mbrennwa/OSDEHA/documentation/figures/CCS_Rsense_circuit.pdf

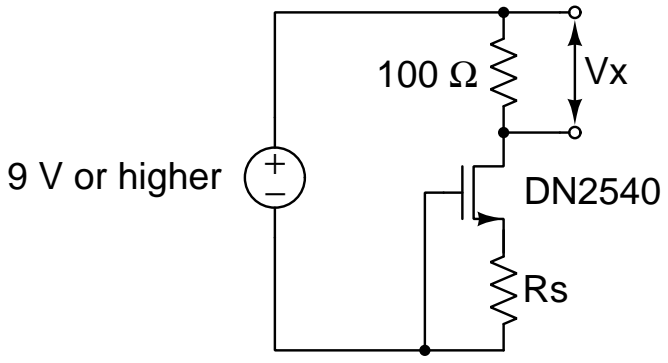
[picture p31: figure]
9 V or higher
