mbrennwa/OSDEHA/documentation/figures/6E5P_curves.pdf

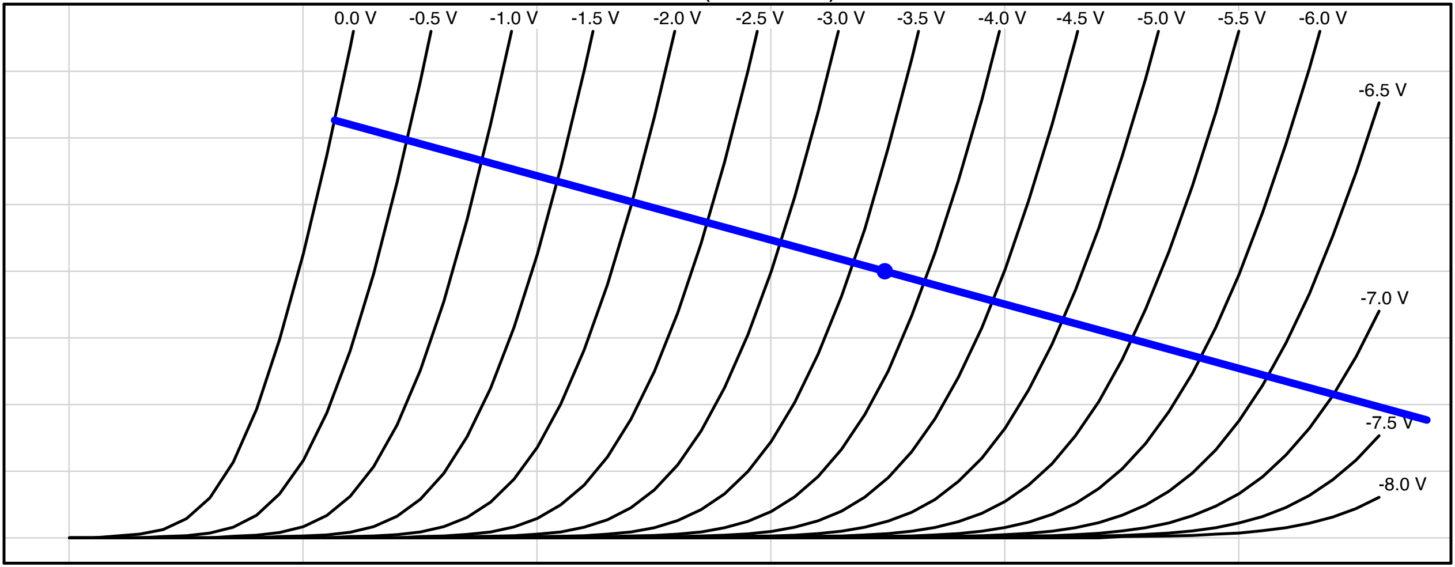
[picture p32: figure]

0 | 50 | 100 | 150 | 200 | 250

## ANODE-CATHODE VOLTAGE (V)

0.0

2.5

5.0

7.5

10.0

12.5

15.0

17.5

20.0

## ANODE CURRENT (mA)

0.0 V -0.5 V -1.0 V | -1.5 V -2.0 V -2.5 V | -3.0 V -3.5 V -4.0 V | -4.5 V -5.0 V -5.5 V | -6.0 V

# 6E5P (TRIODE)
