mbrennwa/OSDEHA/documentation/figures/activeload_concept.pdf

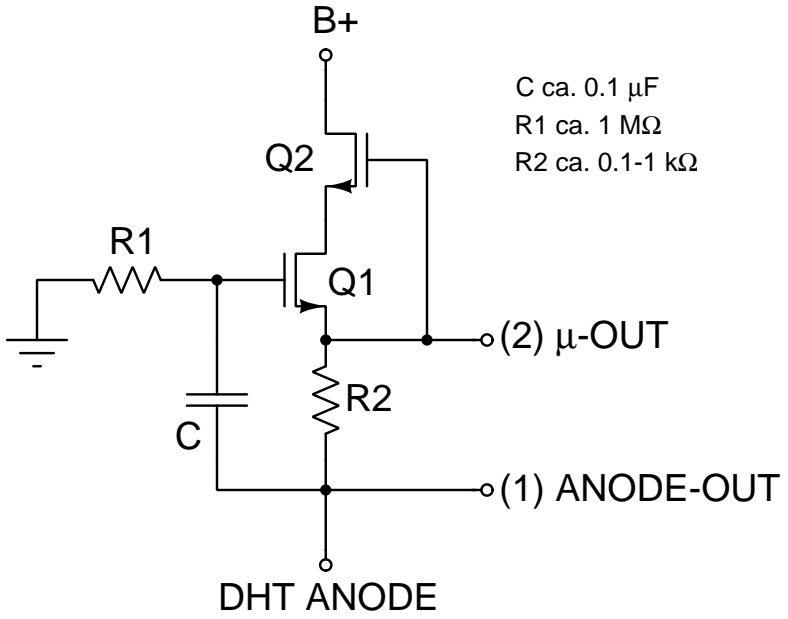
[picture p33: figure]
DHT ANODE; (2) µ-OUT; (1) ANODE-OUT
