mbrennwa/OSDEHA/datasheets/6E5P_curves.webp

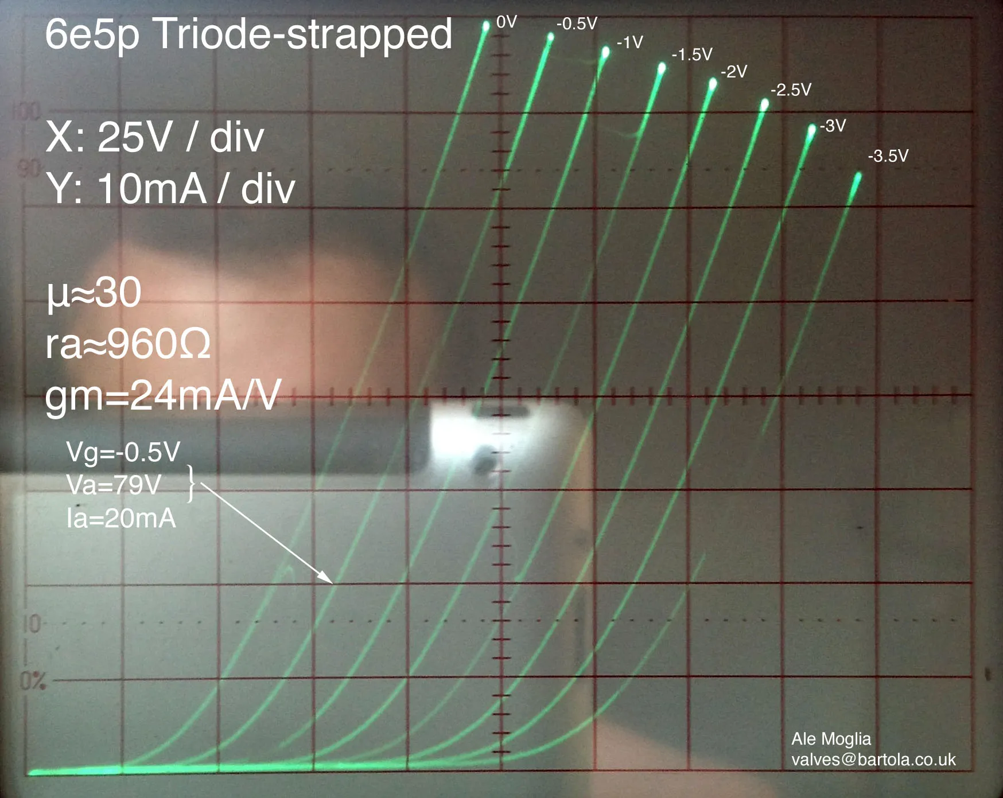
datasheets/6E5P_curves.webp
