mbrennwa/OSDEHA/datasheets/801A_Curves.png

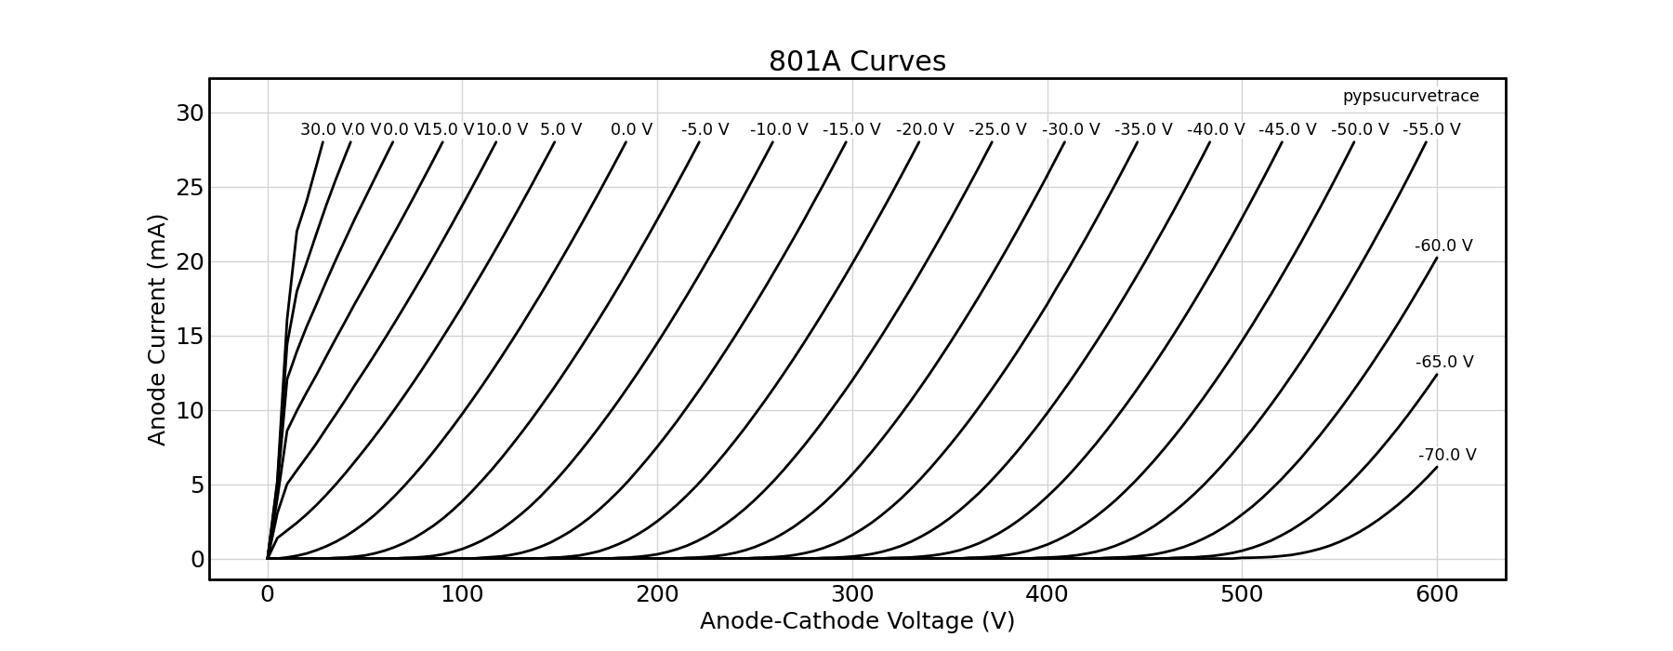
datasheets/801A_Curves.png
