mbrennwa/OSDEHA/datasheets/E180F_curves.png

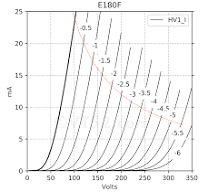
datasheets/E180F_curves.png
