mbrennwa/OSDEHA/datasheets/EF184_curves.jpg

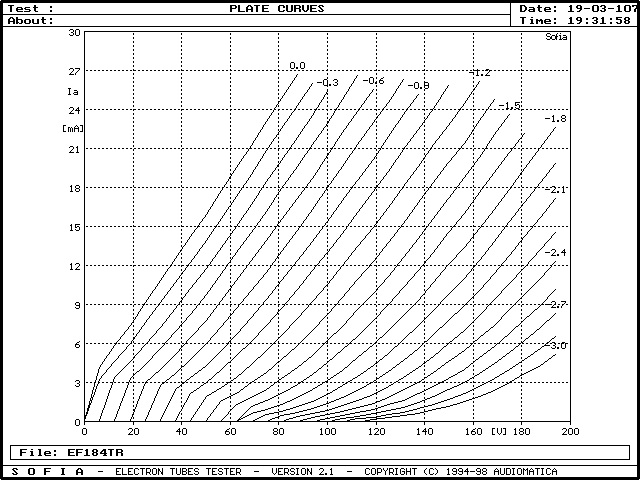
datasheets/EF184_curves.jpg
