mbrennwa/OSDEHA/datasheets/VT25_Curves.png

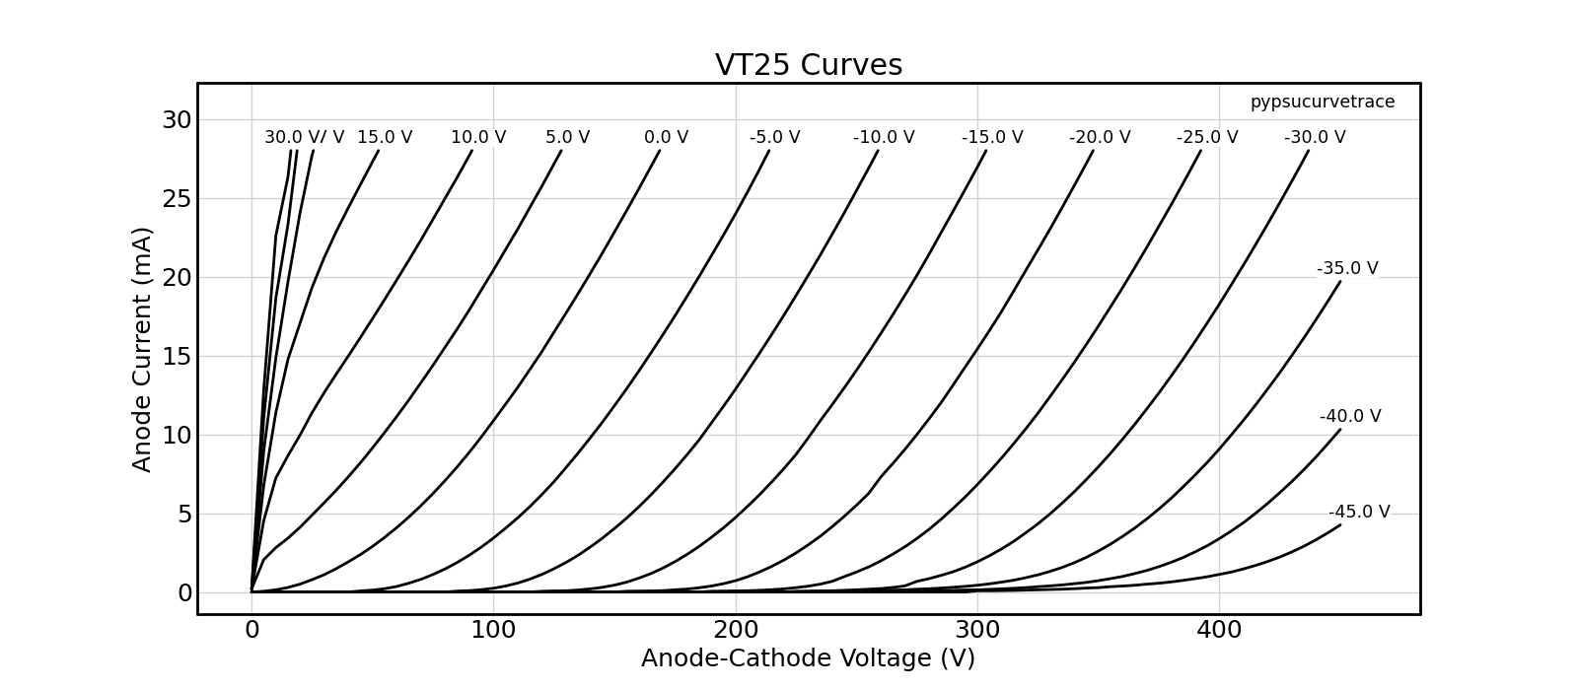
datasheets/VT25_Curves.png
