mbrennwa/OSDEHA/photos/DHT_gate_resistor_on_socket.jpg

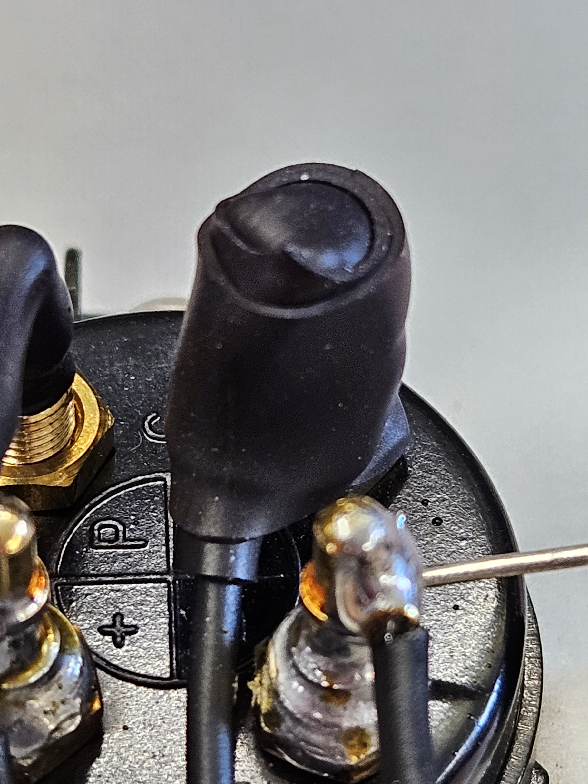
photos/DHT_gate_resistor_on_socket.jpg
