mbrennwa/OSDEHA/stuff/Ale_Moglia_stabilized_HV_for_ideas.webp

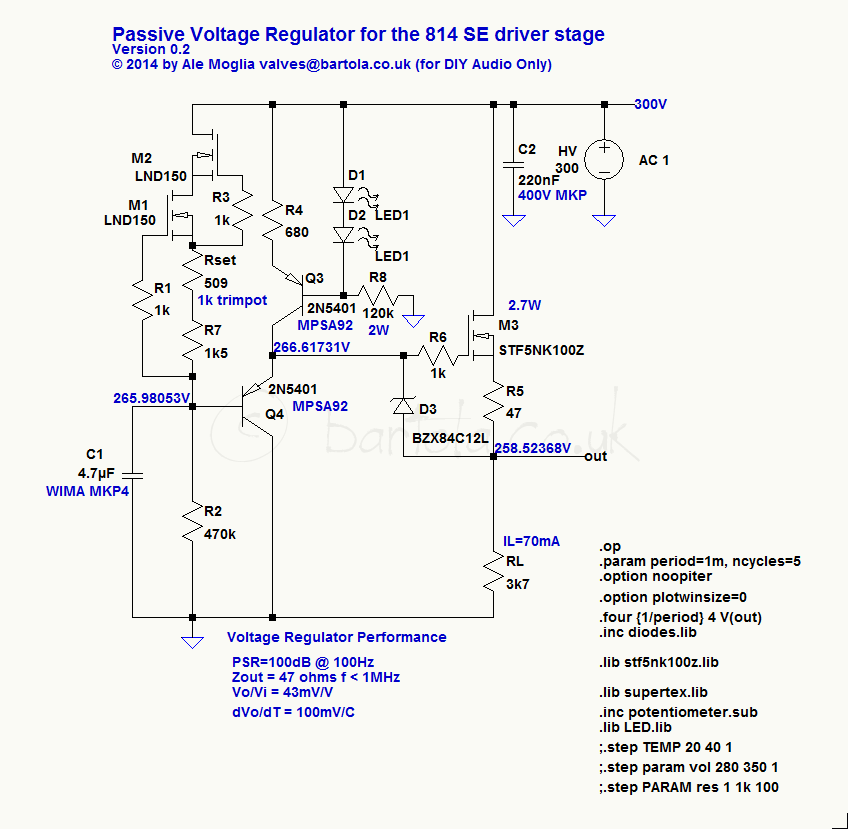
stuff/Ale_Moglia_stabilized_HV_for_ideas.webp
