mbrennwa/OSDEHA/stuff/current_time_physiological_safety/2880px-IEC_TS_60479-1_electric_shock_graph.svg.png

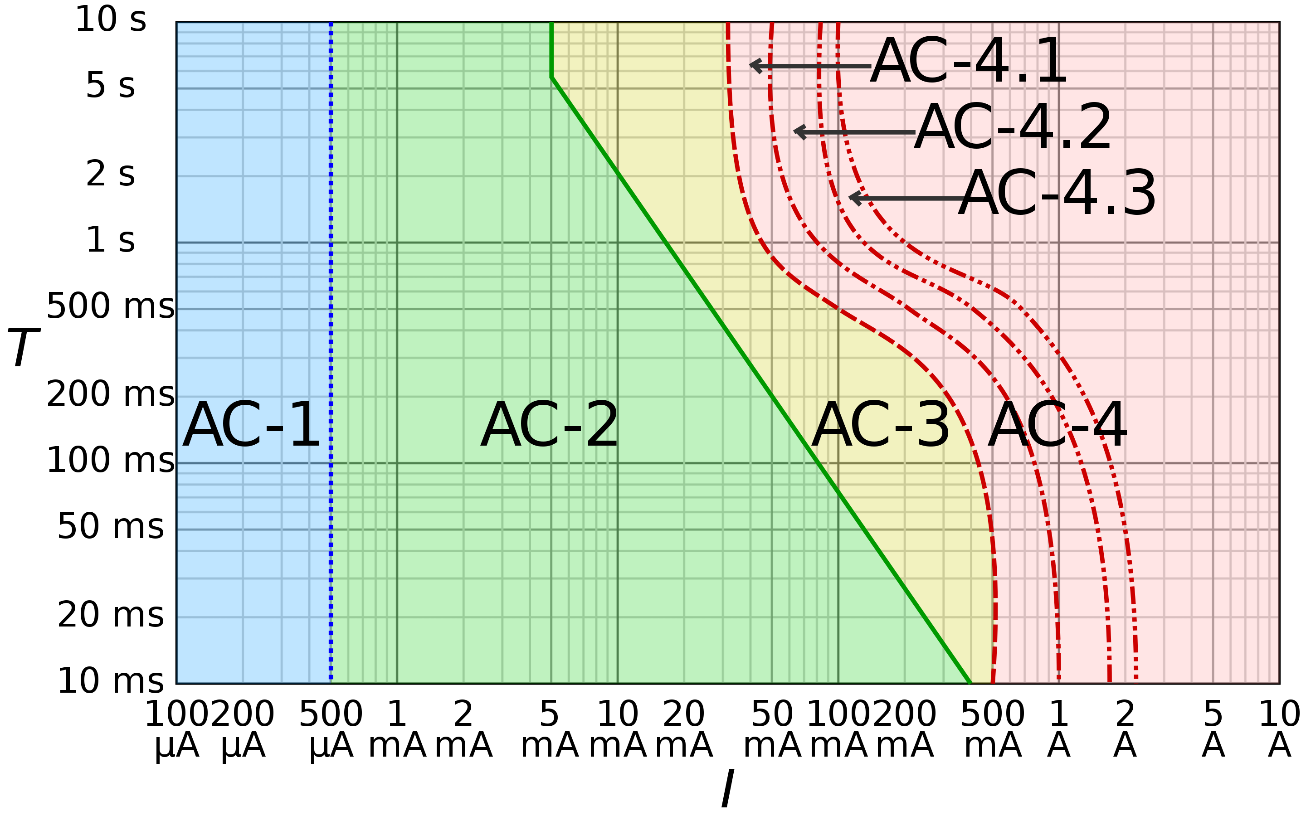
stuff/current_time_physiological_safety/2880px-IEC_TS_60479-1_electric_shock_graph.svg.png
