mbrennwa/OSDEHA/stuff/goldreference_PSU_GRHV_for_ideas.JPG

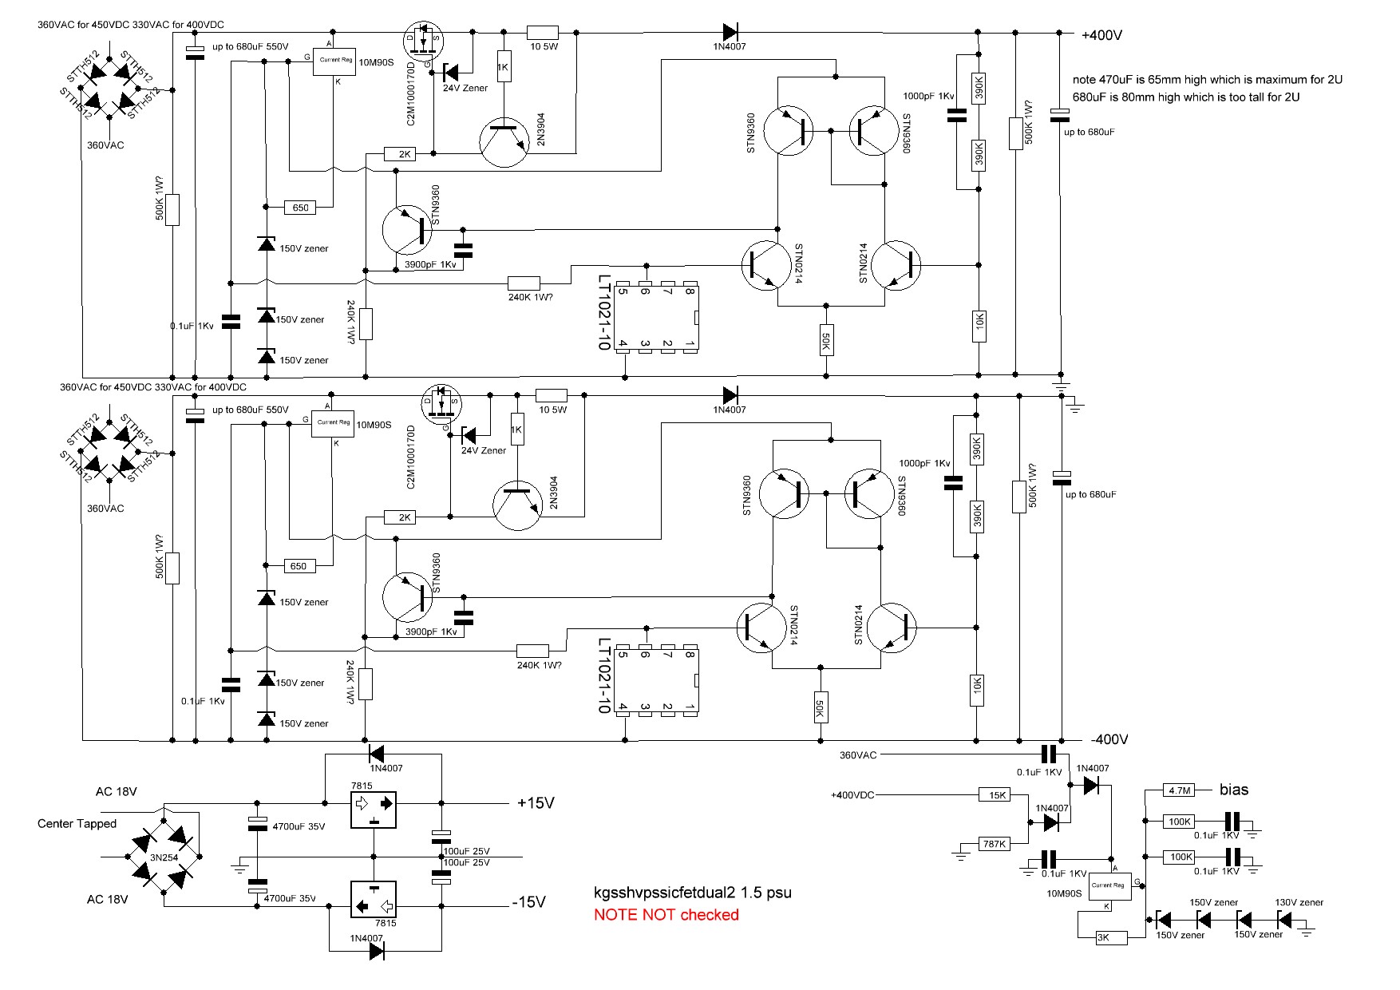
stuff/goldreference_PSU_GRHV_for_ideas.JPG
