mbrennwa/OSDEHA/stuff/rauenbühler_heater_delay_555.GIF

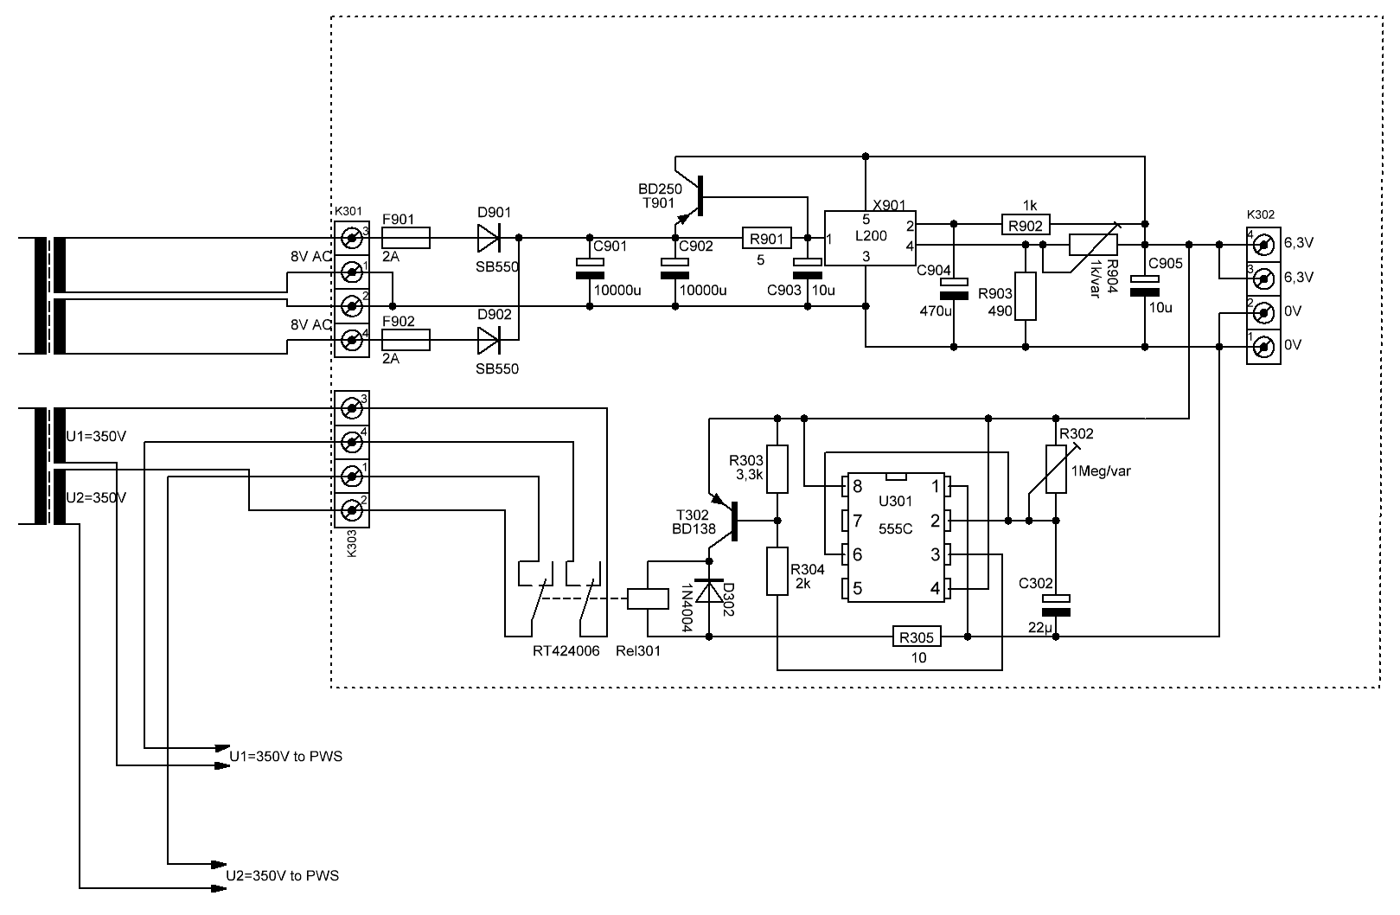
stuff/rauenbühler_heater_delay_555.GIF
