mbrennwa/OSDEHA/notes_and_measurements/2024-05-11/IPS_6E5P_No.5.6_notmatched/OSDEHA_IPS_IM_VOUT31.6.png

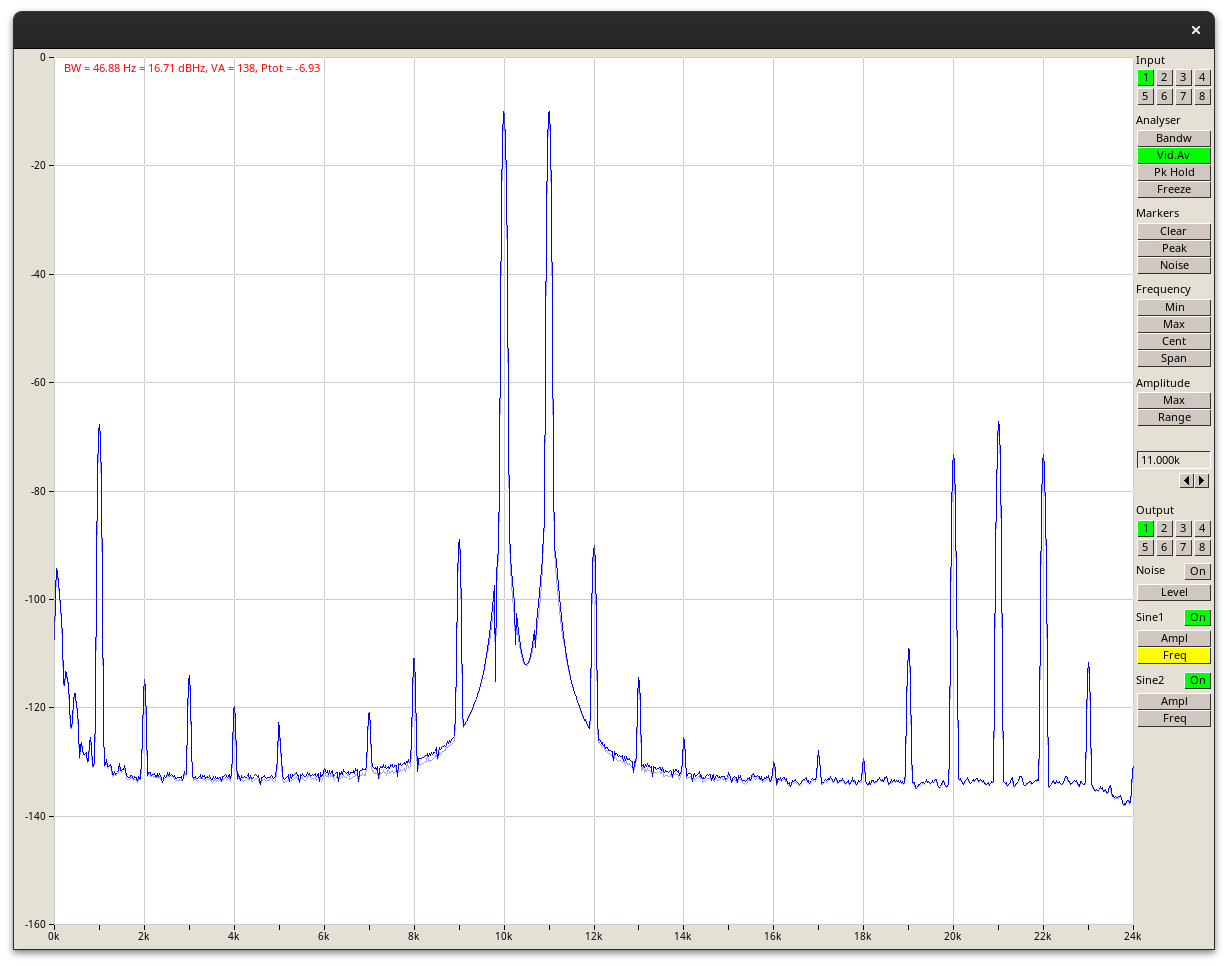
notes_and_measurements/2024-05-11/IPS_6E5P_No.5.6_notmatched/OSDEHA_IPS_IM_VOUT31.6.png
