mbrennwa/OSDEHA/notes_and_measurements/2024-05-11/IPS_6E5P_No.29.34.matched/OSDEHA_IPS_VOUT3.16.png

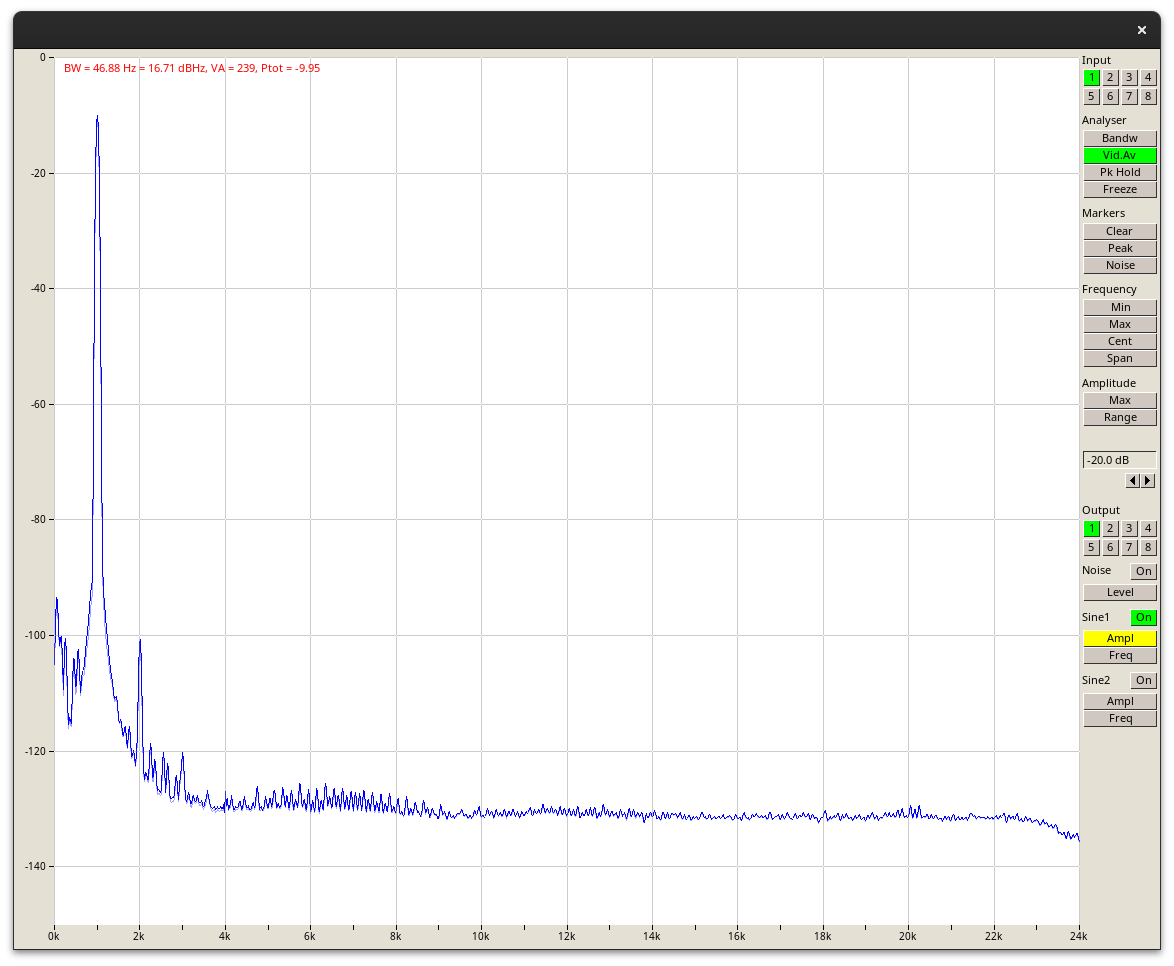
notes_and_measurements/2024-05-11/IPS_6E5P_No.29.34.matched/OSDEHA_IPS_VOUT3.16.png
