mbrennwa/OSDEHA/notes_and_measurements/harmonic_distortion/OSDEHA_MU-out_harmonics-1.png

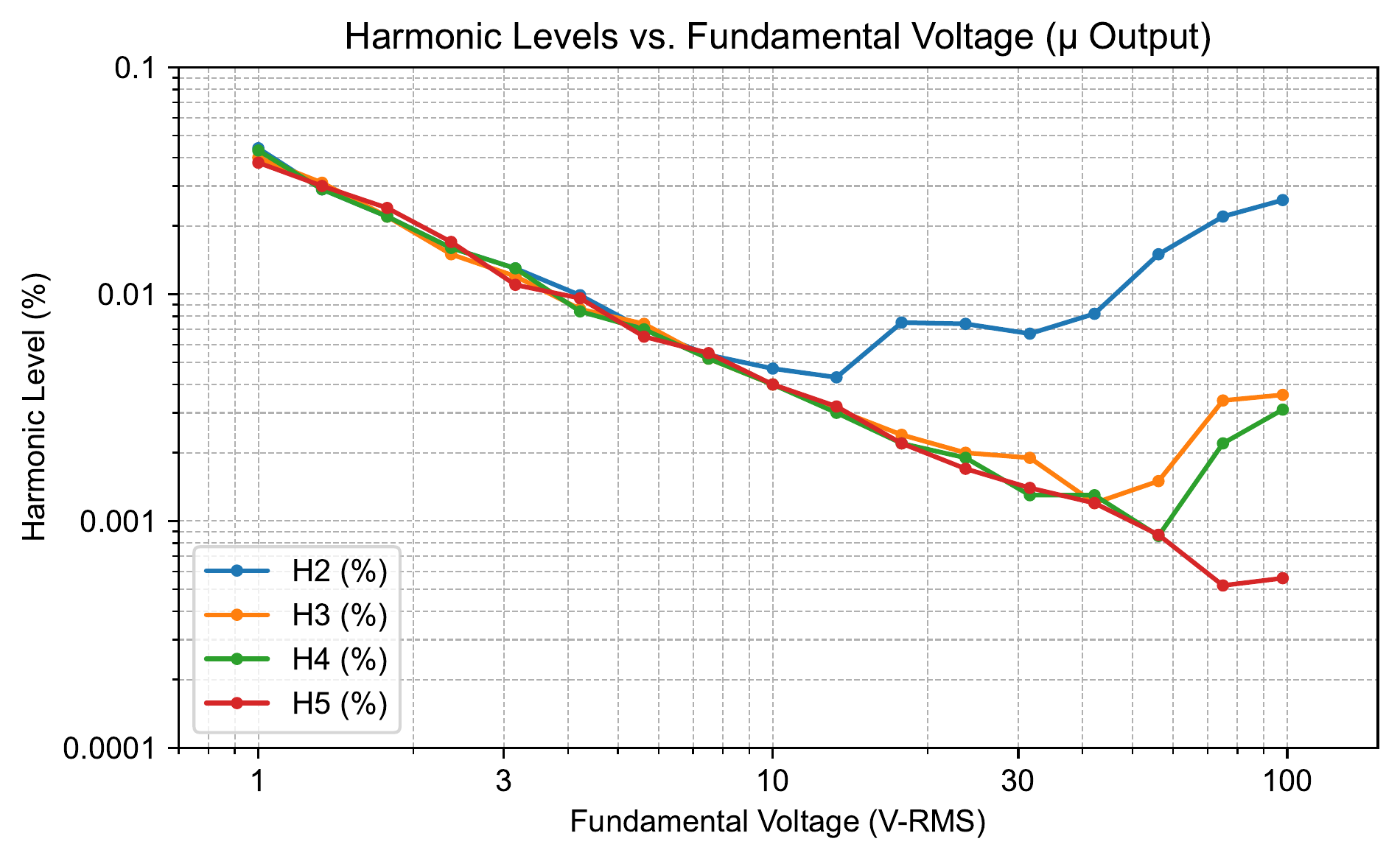
notes_and_measurements/harmonic_distortion/OSDEHA_MU-out_harmonics-1.png
