mbrennwa/OSDEHA/notes_and_measurements/input_tubes/6E5P_Ia10mA_Vg2V_Rk34k.png

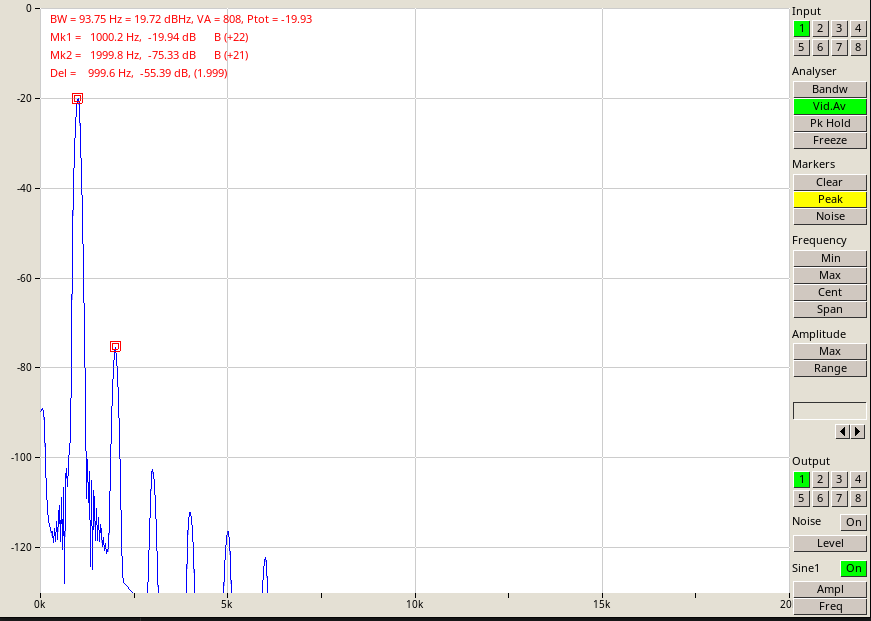
notes_and_measurements/input_tubes/6E5P_Ia10mA_Vg2V_Rk34k.png
