mbrennwa/OSDEHA/notes_and_measurements/input_tubes/6E5P_Ia10mA_Vg3V_Rk28k.png

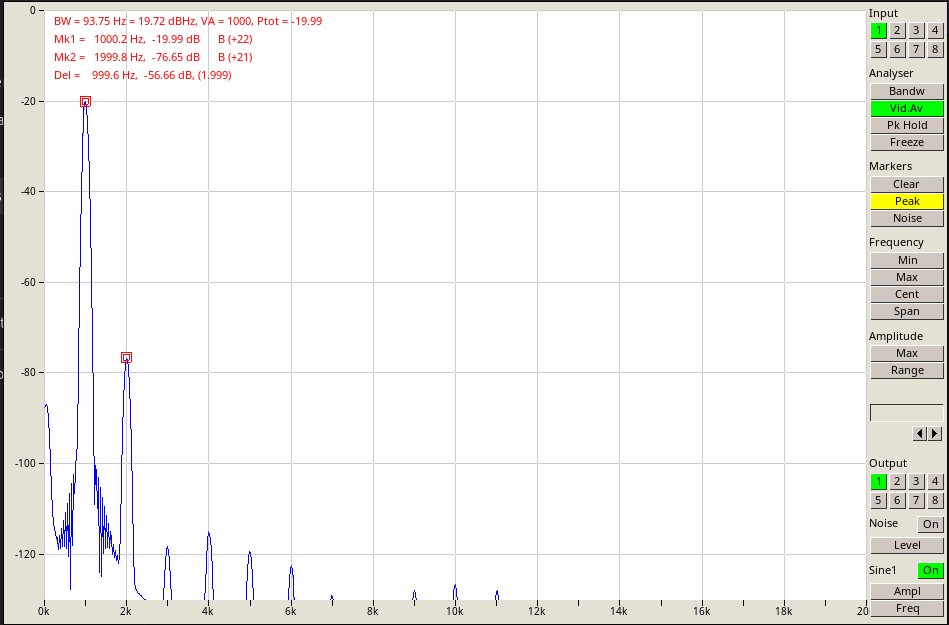
notes_and_measurements/input_tubes/6E5P_Ia10mA_Vg3V_Rk28k.png
