mbrennwa/OSDEHA/documentation/figures/801A_curves.pdf

25

801A

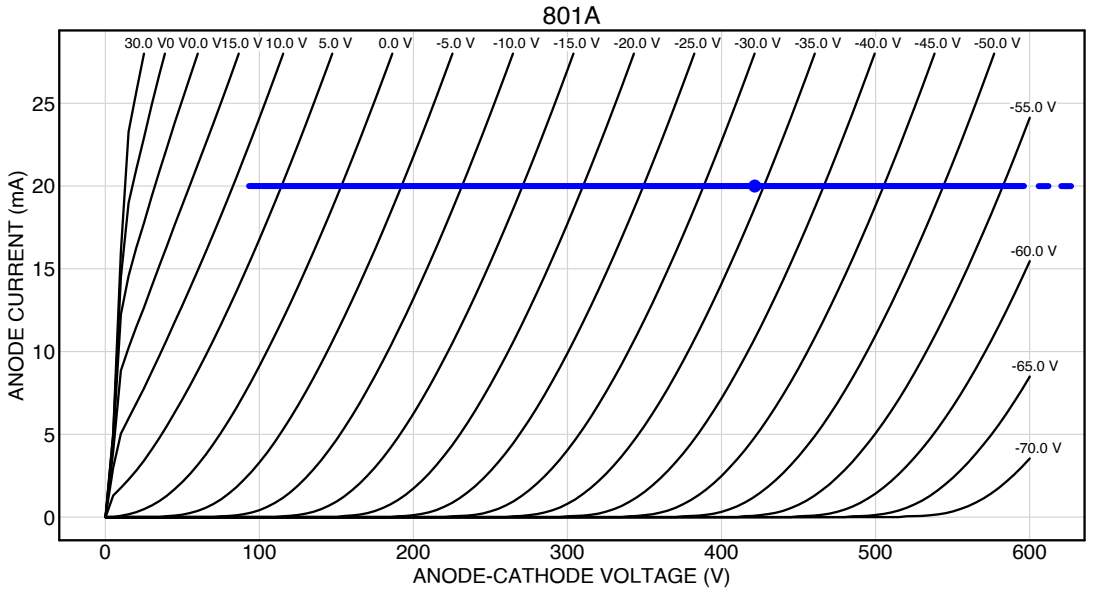
[picture p62: page 1]

ANODE CURRENT (mA)

ANODE-CATHODE VOLTAGE (V)
