mbrennwa/OSDEHA/documentation/figures/OPS_concept.pdf

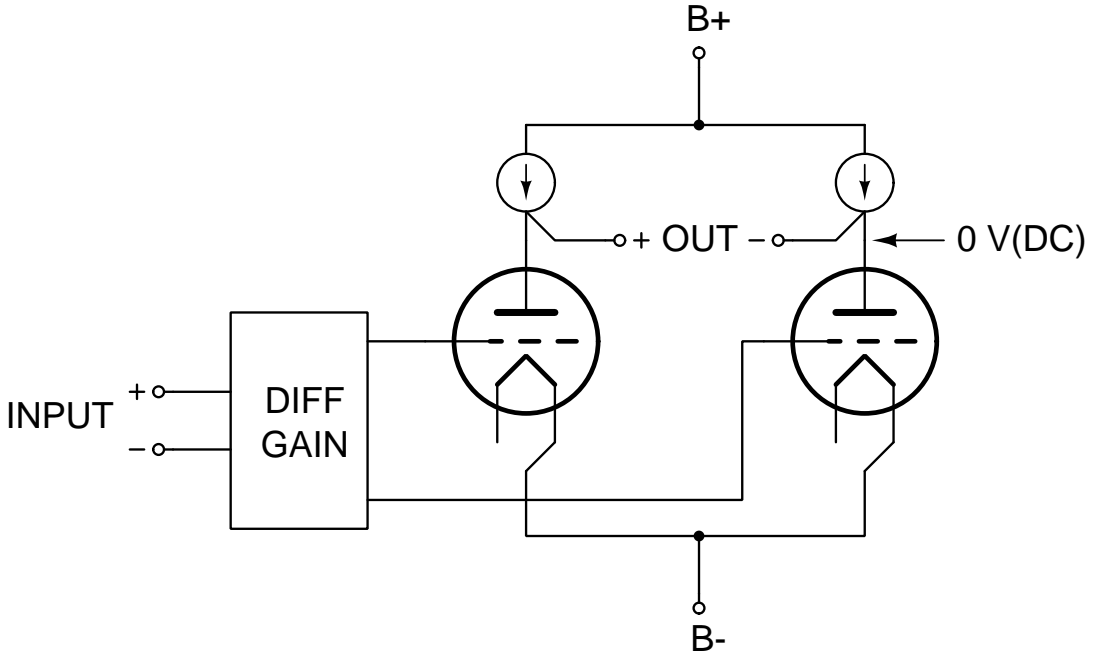
[picture p74: page 1]
OUT; DIFF GAIN; INPUT
