mbrennwa/OSDEHA/stuff/Baby_Huey_for_ideas.pdf

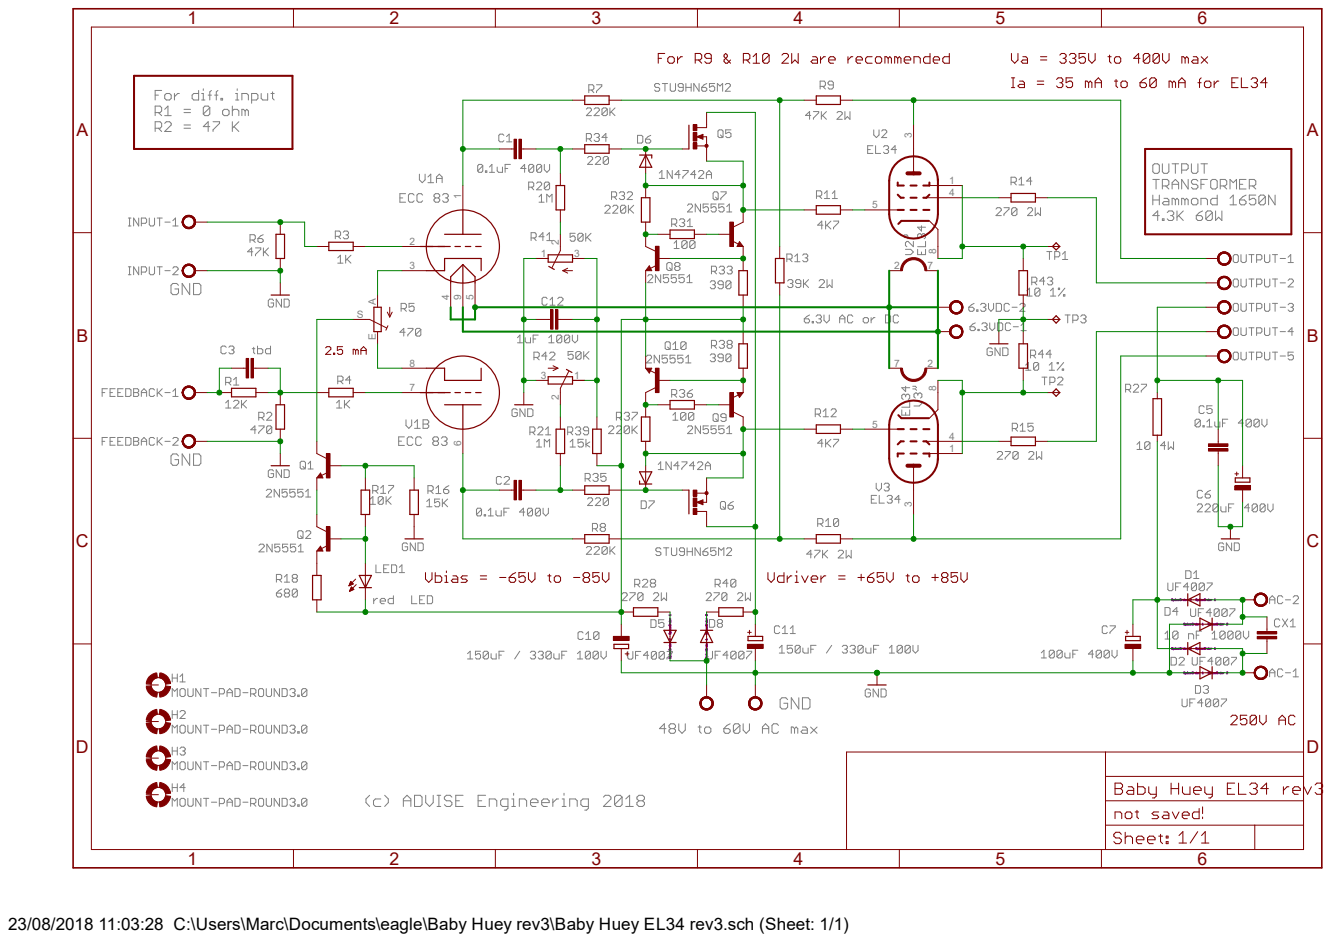
[picture p75: page 1]

23/08/2018 11:03:28 C:\Users\Marc\Documents\eagle\Baby Huey rev3\Baby Huey EL34 rev3.sch (Sheet: 1/1)
