mbrennwa/OSDEHA/documentation/figures/OSDEHA_A-OUT_harmonics_vs_voltage.pdf

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

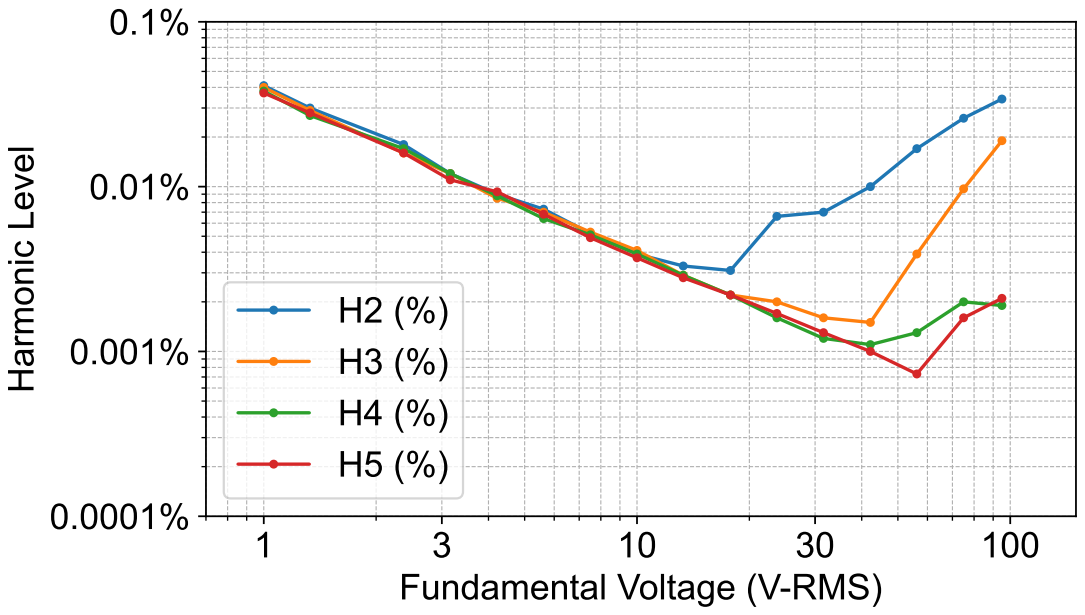
[picture p77: page 1]
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
